austinscreations/Tower-Controller/version 3/CAD/mold rest.stl

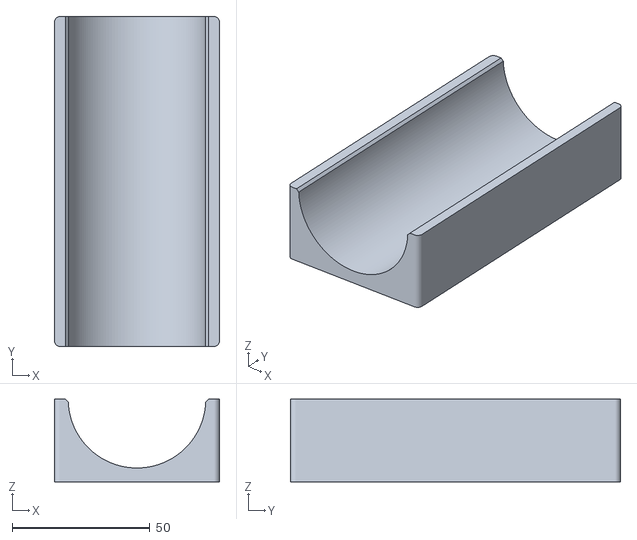
[picture p16: CAD file, 2021-10-31, an earlier design]
version 3/CAD/mold rest.stl
60.0 x 120.0 x 30.0
