austinscreations/Tower-Controller/version 1/computer assembly/computer led panel.stl

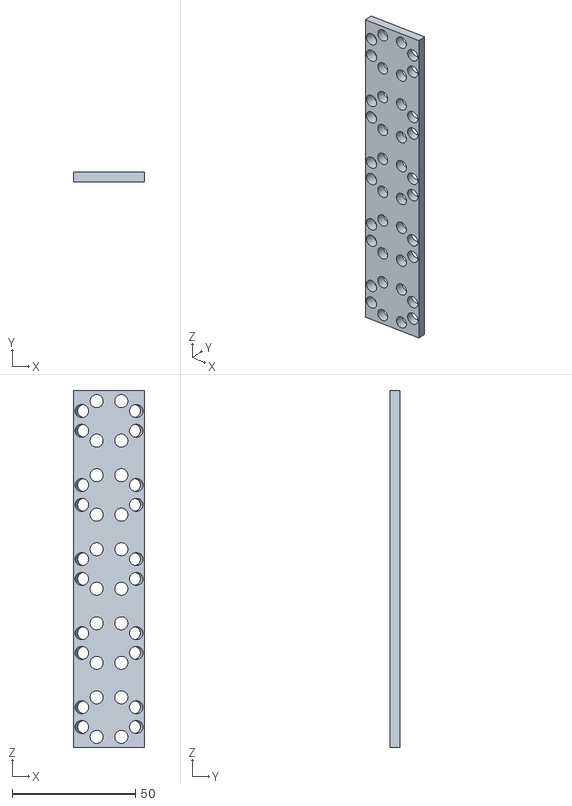
[picture p17: CAD file, 2020-10-23, an earlier design]
version 1/computer assembly/computer led panel.stl
28.6 x 4.00 x 144.6
