austinscreations/Tower-Controller/version 3/CAD/back panel.stl

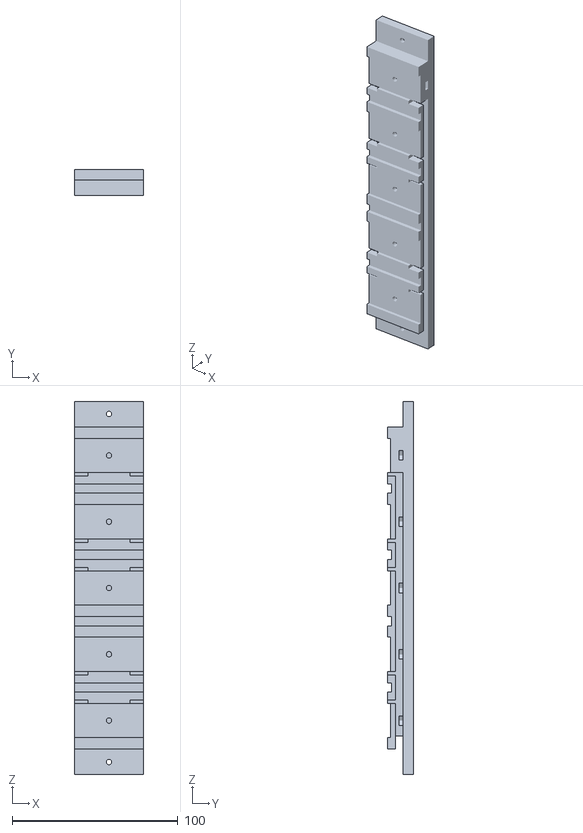
[picture p18: CAD file, 2021-10-31, an earlier design]
version 3/CAD/back panel.stl
41.4 x 15.8 x 225.0
