austinscreations/Tower-Controller/version 3/CAD/tower light.step

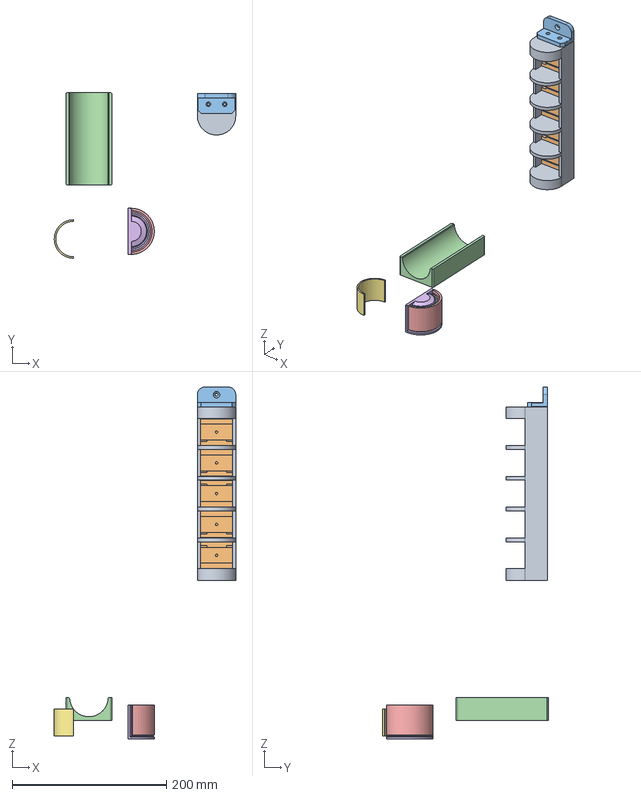
[picture p19: CAD file, 2021-10-31, an earlier design]
version 3/CAD/tower light.step
235.8 x 215.1 x 457.1 mm
